SeeedDocument/Spartan-Edge-Accelerator-Board/img/boot-IDE-2.jpg

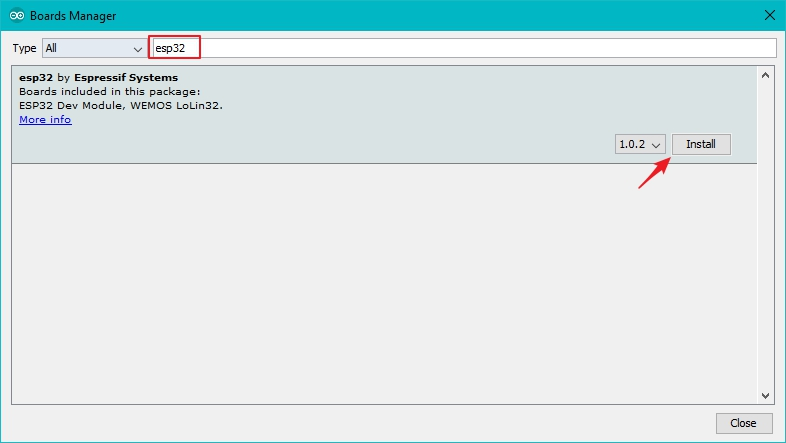
img/boot-IDE-2.jpg
