SeeedDocument/Spartan-Edge-Accelerator-Board/img/Spartan-Edge-Accelerater-Board-v1.0-back.jpg

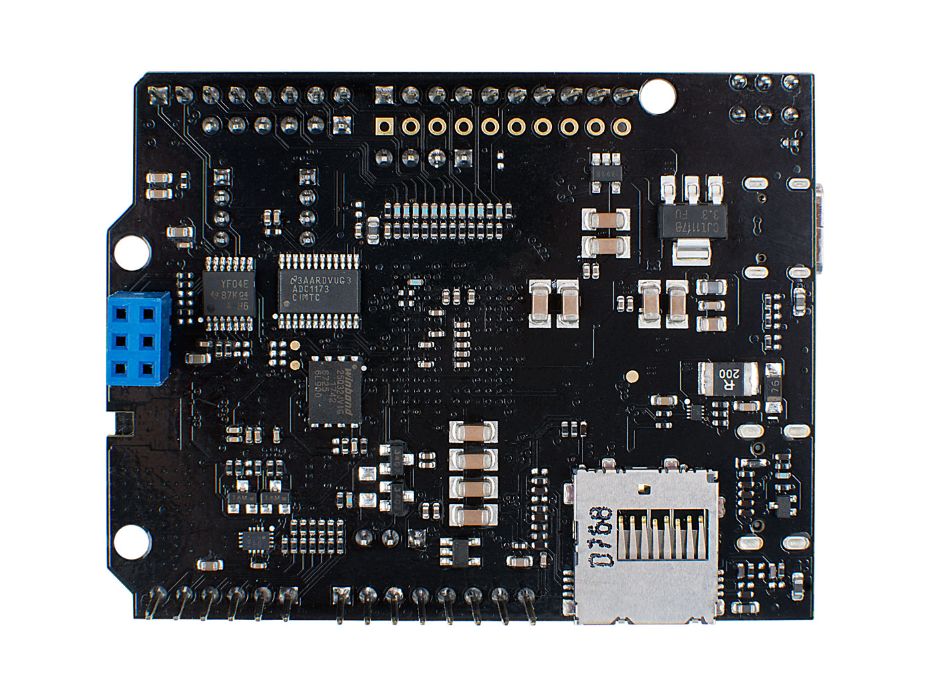
img/Spartan-Edge-Accelerater-Board-v1.0-back.jpg
